RafalBuchner/blastpad/Photos/BlastApp_bw.png

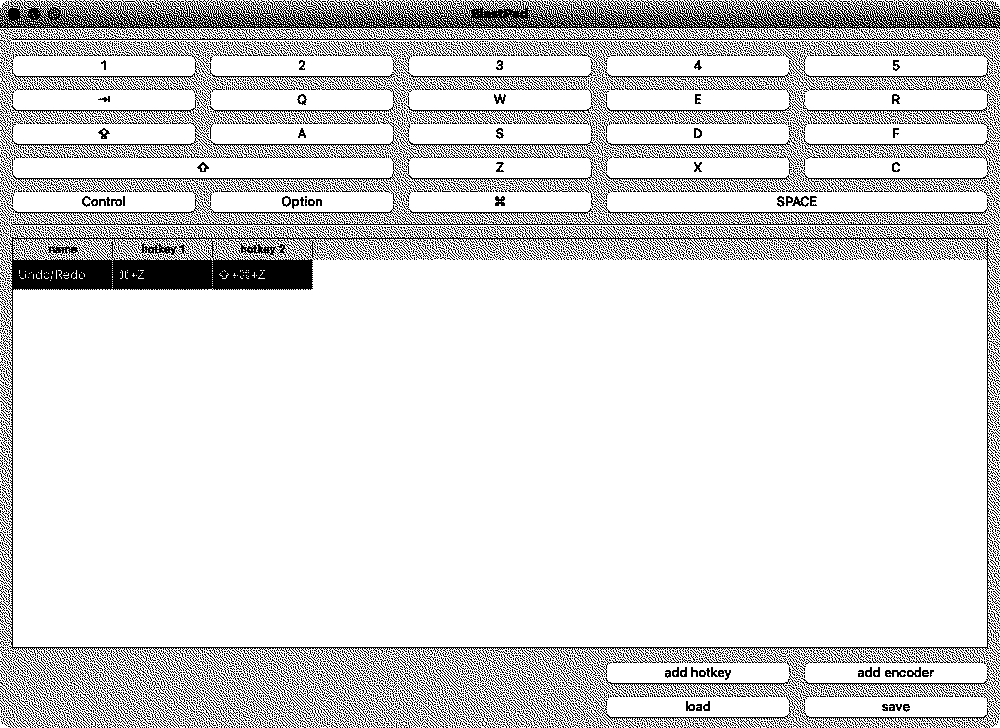
Photos/BlastApp_bw.png
