RafalBuchner/blastpad/resources/package_cover2.png

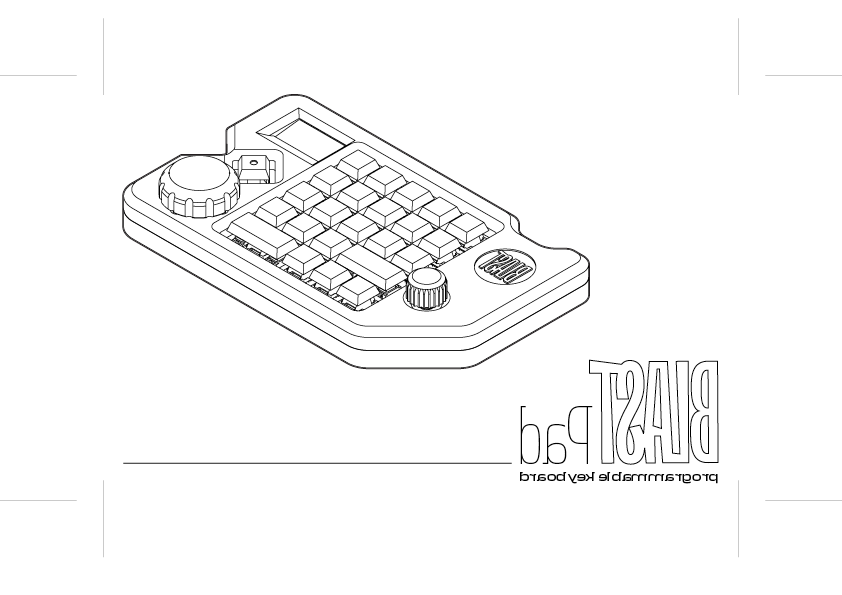
resources/package_cover2.png
